picafe/bicolor-matrix/assets/kicad_k9HAfz9kqA.png

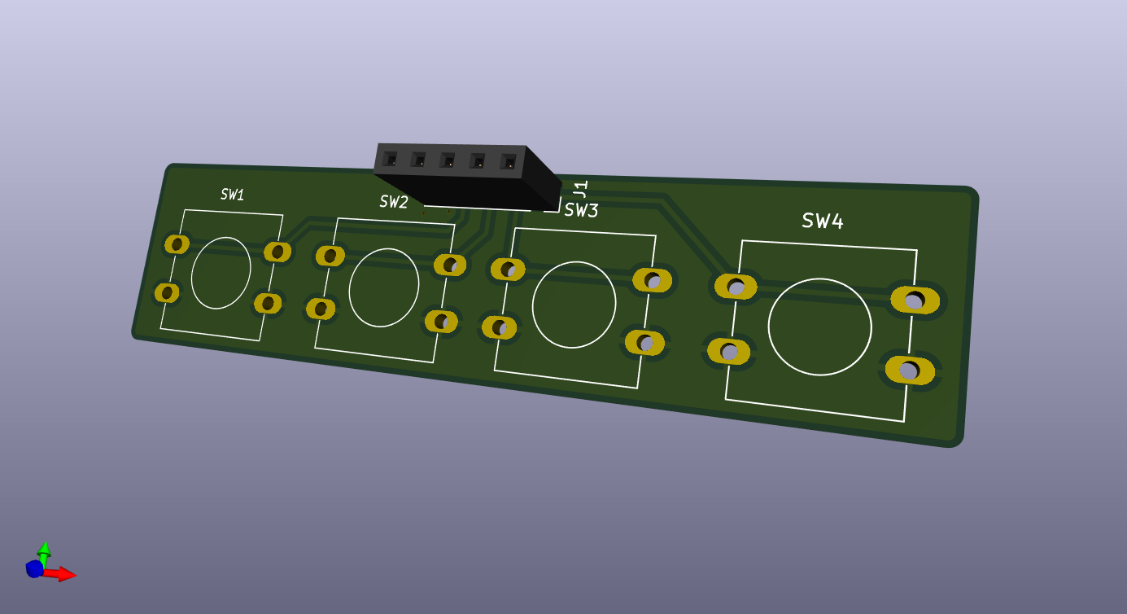
assets/kicad_k9HAfz9kqA.png
